knickers/visualizer-engine/img/2020-01-22 16-57-53.jpg

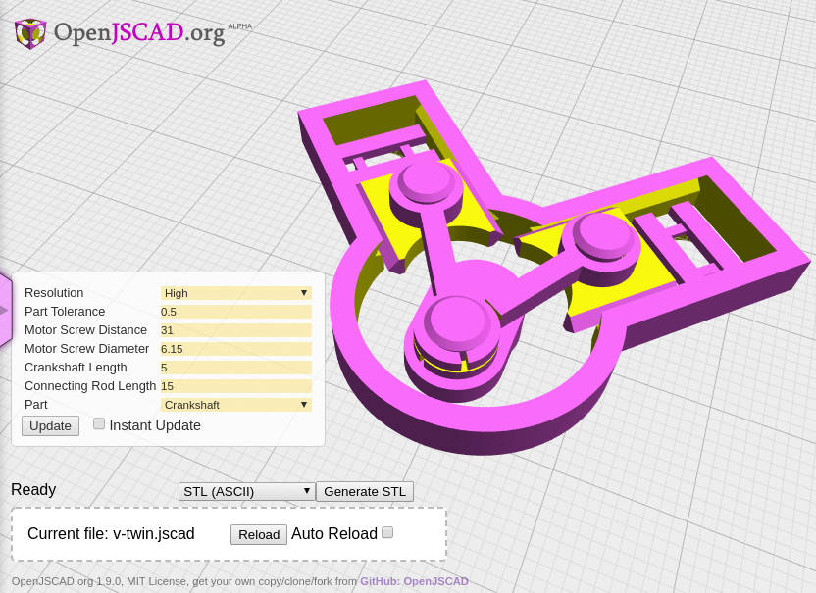
img/2020-01-22 16-57-53.jpg
