knickers/visualizer-engine/img/2020-01-23 09-54-45.jpg

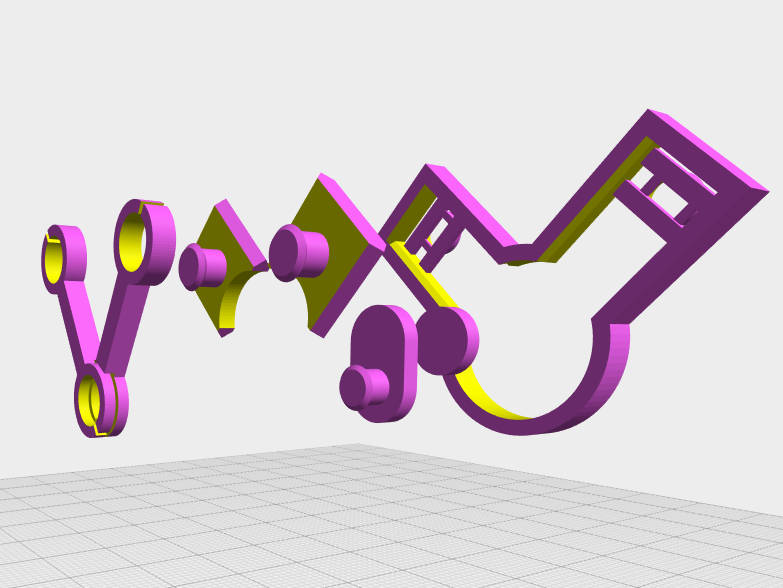
img/2020-01-23 09-54-45.jpg
