knickers/visualizer-engine/img/2020-02-27 14-54-35.jpg

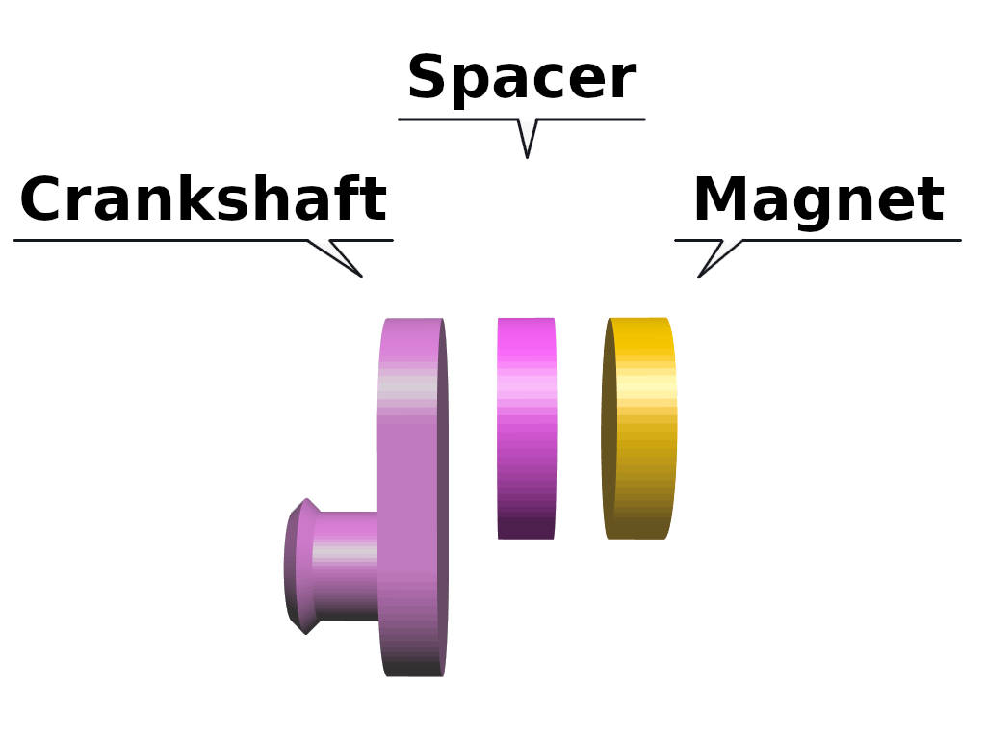
img/2020-02-27 14-54-35.jpg
